ikajdan/katia/hardware/flash.kicad_sch

## KiCad design hardware/flash.kicad_sch (2026-06-07)

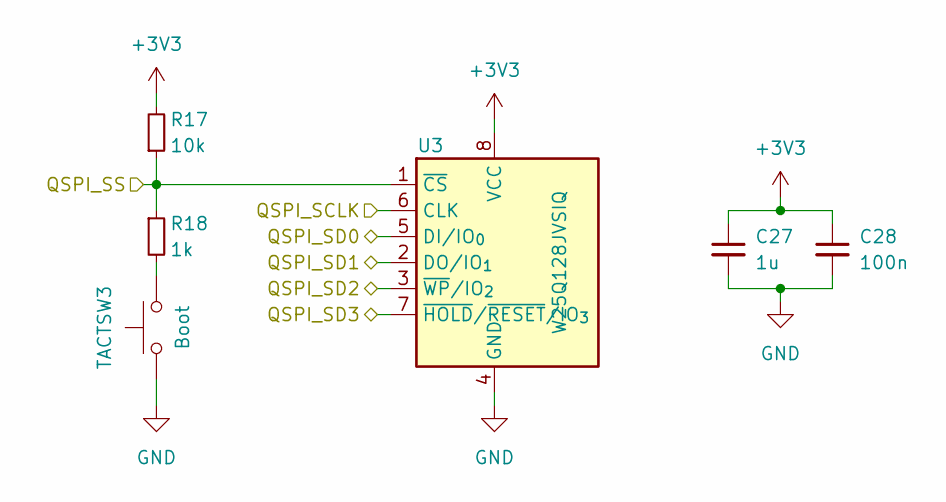
[picture p8: schematic flash.kicad_sch]

Parts:
C27: 1u; C_0603_1608Metric; JLCPCB Part # C15849
C28: 100n; C_0603_1608Metric; JLCPCB Part # C14663
R17: 10k; R_0603_1608Metric; JLCPCB Part # C98220
R18: 1k; R_0603_1608Metric; JLCPCB Part # C22548
TACTSW3: TS-1088R-02026; JLCPCB Part # C455280
U3: W25Q128JVSIQ; SOIC-8_5.3x5.3mm_P1.27mm; JLCPCB Part # C113767

Connections:
+3V3: C27.1, C28.1, R17.2, U3.8 (VCC)
GND: C27.2, C28.2, TACTSW3.1, U3.4 (GND)
unnamed: R18.2, TACTSW3.2
QSPI_SCLK: U3.6 (CLK)
QSPI_SD0: U3.5 (DI/IO_{0})
QSPI_SD1: U3.2 (DO/IO_{1})
QSPI_SD2: U3.3 (~WP/IO_{2})
QSPI_SD3: U3.7 (~HOLD/~RESET/IO_{3})
QSPI_SS: R17.1, R18.1, U3.1 (~CS)
