ikajdan/katia/hardware/leds.kicad_sch

## KiCad design hardware/leds.kicad_sch (2026-06-07)

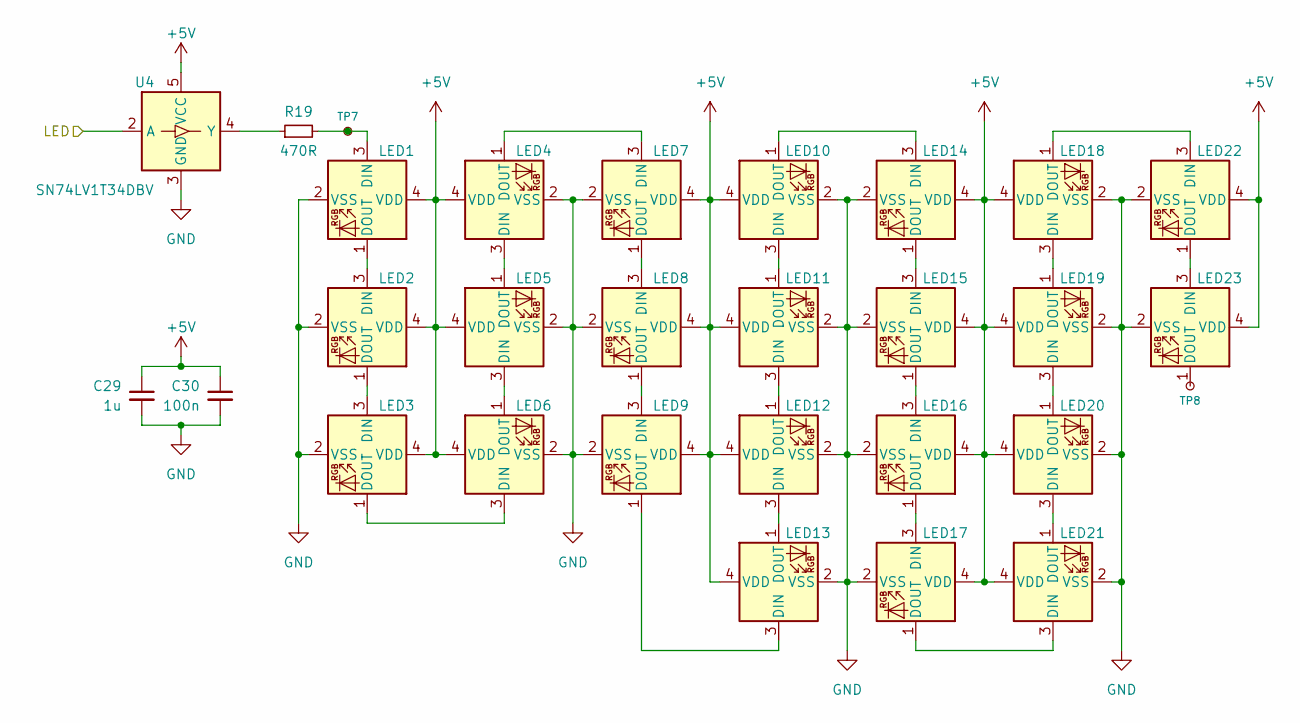
[picture p9: schematic leds.kicad_sch]

Parts:
C29: 1u; C_0603_1608Metric; JLCPCB Part # C15849
C30: 100n; C_0603_1608Metric; JLCPCB Part # C14663
LED1, LED2, LED3, LED4, LED5, LED6, LED7, LED8, LED9, LED10, LED11, LED12, LED13, LED14, LED15, LED16, LED17, LED18, LED19, LED20, LED21, LED22, LED23: YS-SK6812MINI-E; JLCPCB Part # C5149201
R19: 470R; R_0603_1608Metric; JLCPCB Part # C23179
TP7, TP8: TX; TestPoint_Pad_D1.0mm
U4: SN74LV1T34DBV; SOT-23-5; JLCPCB Part # C100024

Connections:
+5V: C29.1, C30.1, LED1.4 (VDD), LED2.4 (VDD), LED3.4 (VDD), LED4.4 (VDD), LED5.4 (VDD), LED6.4 (VDD), LED7.4 (VDD), LED8.4 (VDD), LED9.4 (VDD), LED10.4 (VDD), LED11.4 (VDD), LED12.4 (VDD), LED13.4 (VDD), LED14.4 (VDD), LED15.4 (VDD), LED16.4 (VDD), LED17.4 (VDD), LED18.4 (VDD), LED19.4 (VDD), LED20.4 (VDD), LED21.4 (VDD), LED22.4 (VDD), LED23.4 (VDD), U4.5 (VCC)
GND: C29.2, C30.2, LED1.2 (VSS), LED2.2 (VSS), LED3.2 (VSS), LED4.2 (VSS), LED5.2 (VSS), LED6.2 (VSS), LED7.2 (VSS), LED8.2 (VSS), LED9.2 (VSS), LED10.2 (VSS), LED11.2 (VSS), LED12.2 (VSS), LED13.2 (VSS), LED14.2 (VSS), LED15.2 (VSS), LED16.2 (VSS), LED17.2 (VSS), LED18.2 (VSS), LED19.2 (VSS), LED20.2 (VSS), LED21.2 (VSS), LED22.2 (VSS), LED23.2 (VSS), U4.3 (GND)
LED: U4.2 (A)
unnamed: LED1.1 (DOUT), LED2.3 (DIN)
unnamed: LED1.3 (DIN), R19.2, TP7.1
unnamed: LED2.1 (DOUT), LED3.3 (DIN)
unnamed: LED3.1 (DOUT), LED6.3 (DIN)
unnamed: LED4.1 (DOUT), LED7.3 (DIN)
unnamed: LED4.3 (DIN), LED5.1 (DOUT)
unnamed: LED5.3 (DIN), LED6.1 (DOUT)
unnamed: LED7.1 (DOUT), LED8.3 (DIN)
unnamed: LED8.1 (DOUT), LED9.3 (DIN)
unnamed: LED10.1 (DOUT), LED14.3 (DIN)
unnamed: LED10.3 (DIN), LED11.1 (DOUT)
unnamed: LED11.3 (DIN), LED12.1 (DOUT)
unnamed: LED12.3 (DIN), LED13.1 (DOUT)
unnamed: LED9.1 (DOUT), LED13.3 (DIN)
unnamed: LED14.1 (DOUT), LED15.3 (DIN)
unnamed: LED15.1 (DOUT), LED16.3 (DIN)
unnamed: LED16.1 (DOUT), LED17.3 (DIN)
unnamed: LED17.1 (DOUT), LED21.3 (DIN)
unnamed: LED18.1 (DOUT), LED22.3 (DIN)
unnamed: LED18.3 (DIN), LED19.1 (DOUT)
unnamed: LED19.3 (DIN), LED20.1 (DOUT)
unnamed: LED20.3 (DIN), LED21.1 (DOUT)
unnamed: LED22.1 (DOUT), LED23.3 (DIN)
unnamed: LED23.1 (DOUT), TP8.1
unnamed: R19.1, U4.4 (Y)
