ikajdan/katia/hardware/left_board.kicad_sch

## KiCad design hardware/left_board.kicad_sch (2026-06-07)

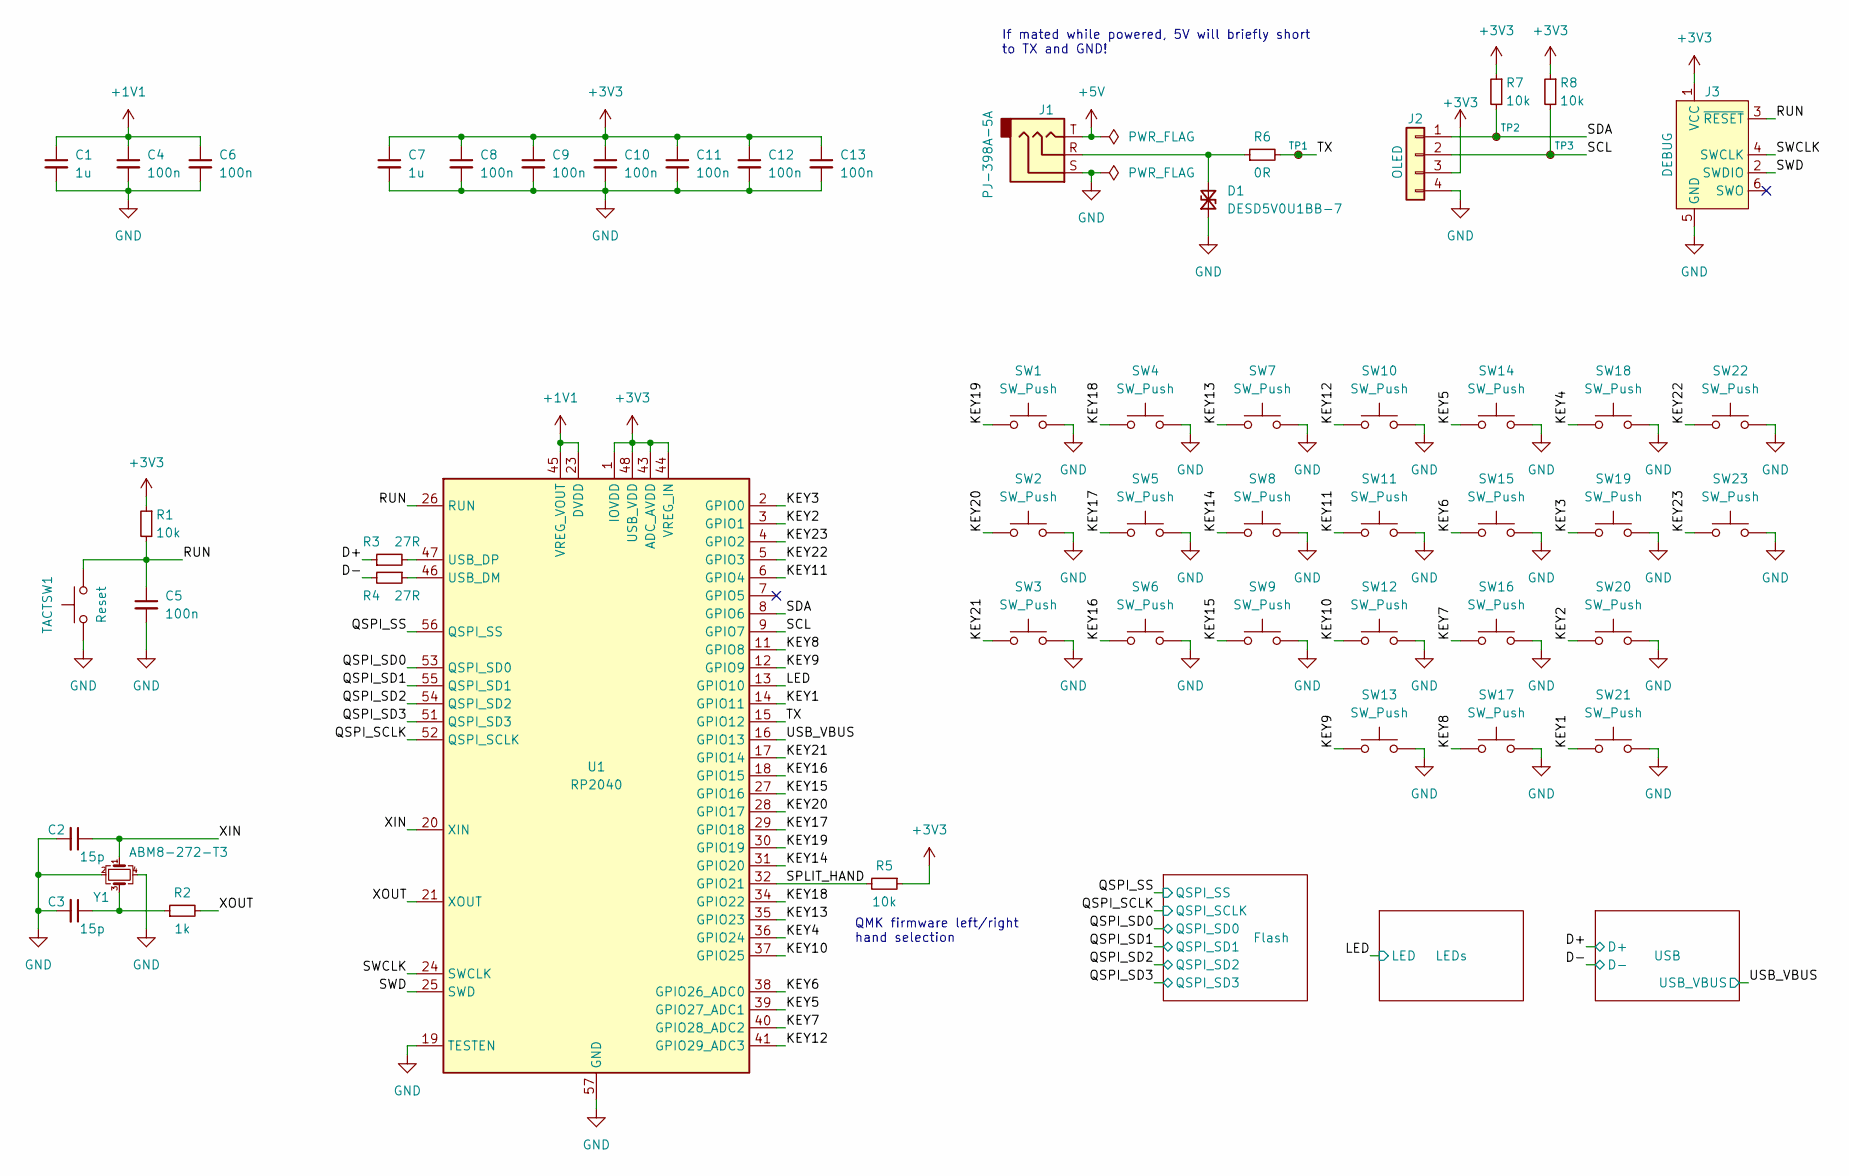
[picture p10: schematic left_board.kicad_sch]

Parts:
C1, C7: 1u; C_0603_1608Metric; JLCPCB Part # C15849
C2, C3: 15p; C_0603_1608Metric; JLCPCB Part # C1644
C4, C5, C6, C8, C9, C10, C11, C12, C13: 100n; C_0603_1608Metric; JLCPCB Part # C14663
D1: DESD5V0U1BB-7; D_SOD-523; JLCPCB Part # C3001672
J1: PJ-398A-5A; JLCPCB Part # C707238
J2: Conn_01x04; OLED_Screen
J3: TC2030-NL; Tag-Connect_TC2030-IDC-NL_2x03_P1.27mm_Vertical
R1, R5, R7, R8: 10k; R_0603_1608Metric; JLCPCB Part # C98220
R2: 1k; R_0603_1608Metric; JLCPCB Part # C22548
R3, R4: 27R; R_0603_1608Metric; JLCPCB Part # C25190
R6: 0R; R_0603_1608Metric; JLCPCB Part # C713447
SW1, SW2, SW3, SW4, SW5, SW6, SW7, SW8, SW9, SW10, SW11, SW12, SW13, SW14, SW15, SW16, SW17, SW18, SW19, SW20, SW22, SW23: SW_Push; SW_Cherry-MX_Hotswap_1u
SW21: SW_Push; SW_Cherry-MX_Hotswap_1.5u
TACTSW1: TS-1088R-02026; JLCPCB Part # C455280
TP1: TX; TestPoint_Pad_D1.0mm
TP2: SDA; TestPoint_Pad_D1.0mm
TP3: SCL; TestPoint_Pad_D1.0mm
U1: RP2040; QFN-56-1EP_7x7mm_P0.4mm_EP3.2x3.2mm; JLCPCB Part # C2040
Y1: ABM8-272-T3; Crystal_SMD_3225-4Pin_3.2x2.5mm; MFR.Part # Q22FA23V0041800; JLCPCB Part # C91749

Connections:
+1V1: C1.1, C4.1, C6.1, U1.23 (DVDD), U1.45 (VREG_VOUT), U1.50 (DVDD)
+3V3: C7.1, C8.1, C9.1, C10.1, C11.1, C12.1, C13.1, J2.3, J3.1 (VCC), R1.1, R5.1, R7.1, R8.1, U1.1 (IOVDD), U1.10 (IOVDD), U1.22 (IOVDD), U1.33 (IOVDD), U1.42 (IOVDD), U1.43 (ADC_AVDD), U1.44 (VREG_IN), U1.48 (USB_VDD), U1.49 (IOVDD)
+5V: J1.T
D+: R3.1
D-: R4.2
GND: C1.2, C2.2, C3.2, C4.2, C5.2, C6.2, C7.2, C8.2, C9.2, C10.2, C11.2, C12.2, C13.2, D1.1 (A1), J1.S, J2.4, J3.5 (GND), SW1.2, SW2.2, SW3.2, SW4.2, SW5.2, SW6.2, SW7.2, SW8.2, SW9.2, SW10.2, SW11.2, SW12.2, SW13.2, SW14.2, SW15.2, SW16.2, SW17.2, SW18.2, SW19.2, SW20.2, SW21.2, SW22.2, SW23.2, TACTSW1.1, U1.19 (TESTEN), U1.57 (GND), Y1.2, Y1.4
KEY1: SW21.1, U1.14 (GPIO11)
KEY2: SW20.1, U1.3 (GPIO1)
KEY3: SW19.1, U1.2 (GPIO0)
KEY4: SW18.1, U1.36 (GPIO24)
KEY5: SW14.1, U1.39 (GPIO27_ADC1)
KEY6: SW15.1, U1.38 (GPIO26_ADC0)
KEY7: SW16.1, U1.40 (GPIO28_ADC2)
KEY8: SW17.1, U1.11 (GPIO8)
KEY9: SW13.1, U1.12 (GPIO9)
KEY10: SW12.1, U1.37 (GPIO25)
KEY11: SW11.1, U1.6 (GPIO4)
KEY12: SW10.1, U1.41 (GPIO29_ADC3)
KEY13: SW7.1, U1.35 (GPIO23)
KEY14: SW8.1, U1.31 (GPIO20)
KEY15: SW9.1, U1.27 (GPIO16)
KEY16: SW6.1, U1.18 (GPIO15)
KEY17: SW5.1, U1.29 (GPIO18)
KEY18: SW4.1, U1.34 (GPIO22)
KEY19: SW1.1, U1.30 (GPIO19)
KEY20: SW2.1, U1.28 (GPIO17)
KEY21: SW3.1, U1.17 (GPIO14)
KEY22: SW22.1, U1.5 (GPIO3)
KEY23: SW23.1, U1.4 (GPIO2)
LED: U1.13 (GPIO10)
unnamed: C3.1, R2.1, Y1.3
unnamed: D1.2 (A2), J1.R, R6.1
unnamed: R3.2, U1.47 (USB_DP)
unnamed: R4.1, U1.46 (USB_DM)
QSPI_SCLK: U1.52 (QSPI_SCLK)
QSPI_SD0: U1.53 (QSPI_SD0)
QSPI_SD1: U1.55 (QSPI_SD1)
QSPI_SD2: U1.54 (QSPI_SD2)
QSPI_SD3: U1.51 (QSPI_SD3)
QSPI_SS: U1.56 (QSPI_SS)
RUN: C5.1, J3.3 (~RESET), R1.2, TACTSW1.2, U1.26 (RUN)
SCL: J2.2, R8.2, TP3.1, U1.9 (GPIO7)
SDA: J2.1, R7.2, TP2.1, U1.8 (GPIO6)
SPLIT_HAND: R5.2, U1.32 (GPIO21)
SWCLK: J3.4 (SWCLK), U1.24 (SWCLK)
SWD: J3.2 (SWDIO), U1.25 (SWD)
TX: R6.2, TP1.1, U1.15 (GPIO12)
USB_VBUS: U1.16 (GPIO13)
XIN: C2.1, U1.20 (XIN), Y1.1
XOUT: R2.2, U1.21 (XOUT)

Notes on the sheet:
If mated while powered, 5V will briefly short to TX and GND!
QMK firmware left/right hand selection
