ikajdan/katia/hardware/right_board.kicad_sch

## KiCad design hardware/right_board.kicad_sch (2026-06-07)

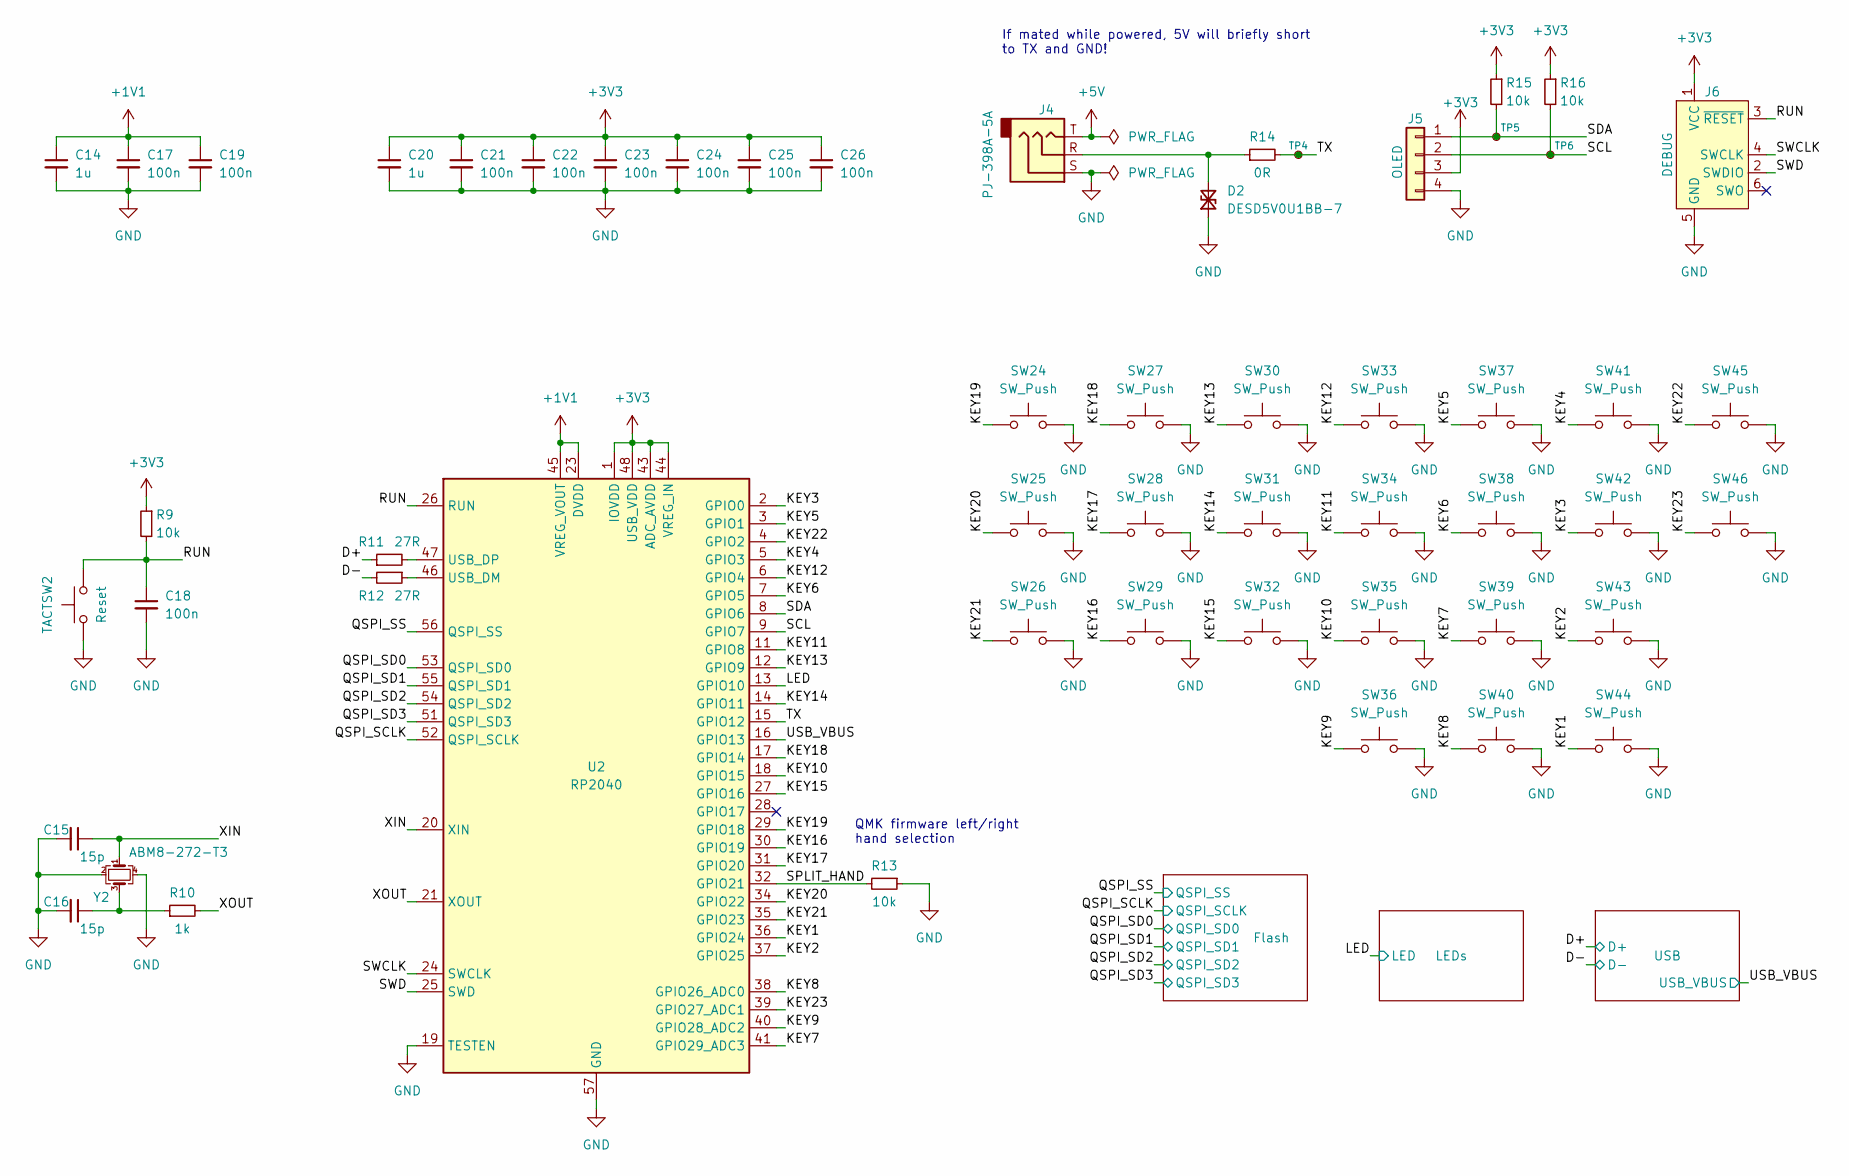
[picture p11: schematic right_board.kicad_sch]

Parts:
C14, C20: 1u; C_0603_1608Metric; JLCPCB Part # C15849
C15, C16: 15p; C_0603_1608Metric; JLCPCB Part # C1644
C17, C18, C19, C21, C22, C23, C24, C25, C26: 100n; C_0603_1608Metric; JLCPCB Part # C14663
D2: DESD5V0U1BB-7; D_SOD-523; JLCPCB Part # C3001672
J4: PJ-398A-5A; JLCPCB Part # C707238
J5: Conn_01x04; OLED_Screen
J6: TC2030-NL; Tag-Connect_TC2030-IDC-NL_2x03_P1.27mm_Vertical
R9, R13, R15, R16: 10k; R_0603_1608Metric; JLCPCB Part # C98220
R10: 1k; R_0603_1608Metric; JLCPCB Part # C22548
R11, R12: 27R; R_0603_1608Metric; JLCPCB Part # C25190
R14: 0R; R_0603_1608Metric; JLCPCB Part # C713447
SW24, SW25, SW26, SW27, SW28, SW29, SW30, SW31, SW32, SW33, SW34, SW35, SW36, SW37, SW38, SW39, SW40, SW41, SW42, SW43, SW45, SW46: SW_Push; SW_Cherry-MX_Hotswap_1u
SW44: SW_Push; SW_Cherry-MX_Hotswap_1.5u
TACTSW2: TS-1088R-02026; JLCPCB Part # C455280
TP4: TX; TestPoint_Pad_D1.0mm
TP5: SDA; TestPoint_Pad_D1.0mm
TP6: SCL; TestPoint_Pad_D1.0mm
U2: RP2040; QFN-56-1EP_7x7mm_P0.4mm_EP3.2x3.2mm; JLCPCB Part # C2040
Y2: ABM8-272-T3; Crystal_SMD_3225-4Pin_3.2x2.5mm; MFR.Part # Q22FA23V0041800; JLCPCB Part # C91749

Connections:
+1V1: C14.1, C17.1, C19.1, U2.23 (DVDD), U2.45 (VREG_VOUT), U2.50 (DVDD)
+3V3: C20.1, C21.1, C22.1, C23.1, C24.1, C25.1, C26.1, J5.3, J6.1 (VCC), R9.1, R15.1, R16.1, U2.1 (IOVDD), U2.10 (IOVDD), U2.22 (IOVDD), U2.33 (IOVDD), U2.42 (IOVDD), U2.43 (ADC_AVDD), U2.44 (VREG_IN), U2.48 (USB_VDD), U2.49 (IOVDD)
+5V: J4.T
D+: R11.1
D-: R12.2
GND: C14.2, C15.2, C16.2, C17.2, C18.2, C19.2, C20.2, C21.2, C22.2, C23.2, C24.2, C25.2, C26.2, D2.1 (A1), J4.S, J5.4, J6.5 (GND), R13.1, SW24.2, SW25.2, SW26.2, SW27.2, SW28.2, SW29.2, SW30.2, SW31.2, SW32.2, SW33.2, SW34.2, SW35.2, SW36.2, SW37.2, SW38.2, SW39.2, SW40.2, SW41.2, SW42.2, SW43.2, SW44.2, SW45.2, SW46.2, TACTSW2.1, U2.19 (TESTEN), U2.57 (GND), Y2.2, Y2.4
KEY1: SW44.1, U2.36 (GPIO24)
KEY2: SW43.1, U2.37 (GPIO25)
KEY3: SW42.1, U2.2 (GPIO0)
KEY4: SW41.1, U2.5 (GPIO3)
KEY5: SW37.1, U2.3 (GPIO1)
KEY6: SW38.1, U2.7 (GPIO5)
KEY7: SW39.1, U2.41 (GPIO29_ADC3)
KEY8: SW40.1, U2.38 (GPIO26_ADC0)
KEY9: SW36.1, U2.40 (GPIO28_ADC2)
KEY10: SW35.1, U2.18 (GPIO15)
KEY11: SW34.1, U2.11 (GPIO8)
KEY12: SW33.1, U2.6 (GPIO4)
KEY13: SW30.1, U2.12 (GPIO9)
KEY14: SW31.1, U2.14 (GPIO11)
KEY15: SW32.1, U2.27 (GPIO16)
KEY16: SW29.1, U2.30 (GPIO19)
KEY17: SW28.1, U2.31 (GPIO20)
KEY18: SW27.1, U2.17 (GPIO14)
KEY19: SW24.1, U2.29 (GPIO18)
KEY20: SW25.1, U2.34 (GPIO22)
KEY21: SW26.1, U2.35 (GPIO23)
KEY22: SW45.1, U2.4 (GPIO2)
KEY23: SW46.1, U2.39 (GPIO27_ADC1)
LED: U2.13 (GPIO10)
unnamed: C16.1, R10.1, Y2.3
unnamed: D2.2 (A2), J4.R, R14.1
unnamed: R11.2, U2.47 (USB_DP)
unnamed: R12.1, U2.46 (USB_DM)
QSPI_SCLK: U2.52 (QSPI_SCLK)
QSPI_SD0: U2.53 (QSPI_SD0)
QSPI_SD1: U2.55 (QSPI_SD1)
QSPI_SD2: U2.54 (QSPI_SD2)
QSPI_SD3: U2.51 (QSPI_SD3)
QSPI_SS: U2.56 (QSPI_SS)
RUN: C18.1, J6.3 (~RESET), R9.2, TACTSW2.2, U2.26 (RUN)
SCL: J5.2, R16.2, TP6.1, U2.9 (GPIO7)
SDA: J5.1, R15.2, TP5.1, U2.8 (GPIO6)
SPLIT_HAND: R13.2, U2.32 (GPIO21)
SWCLK: J6.4 (SWCLK), U2.24 (SWCLK)
SWD: J6.2 (SWDIO), U2.25 (SWD)
TX: R14.2, TP4.1, U2.15 (GPIO12)
USB_VBUS: U2.16 (GPIO13)
XIN: C15.1, U2.20 (XIN), Y2.1
XOUT: R10.2, U2.21 (XOUT)

Notes on the sheet:
If mated while powered, 5V will briefly short to TX and GND!
QMK firmware left/right hand selection
