ikajdan/katia/hardware/usb.kicad_sch

## KiCad design hardware/usb.kicad_sch (2026-06-07)

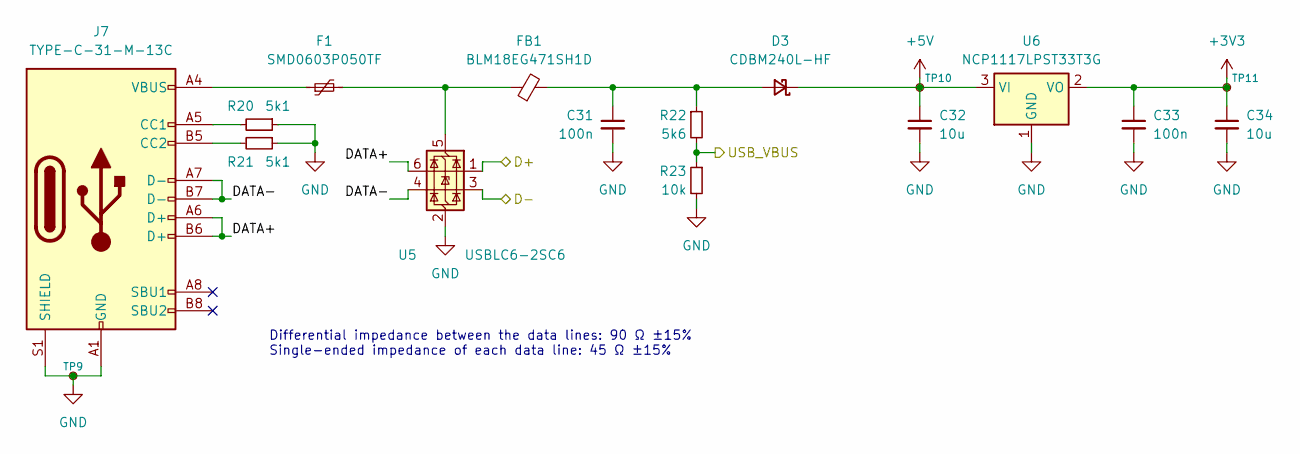
[picture p12: schematic usb.kicad_sch]

Parts:
C31, C33: 100n; C_0603_1608Metric; JLCPCB Part # C14663
C32, C34: 10u; C_0603_1608Metric; JLCPCB Part # C19702
D3: CDBM240L-HF; D_SOD-123; JLCPCB Part # C3012684
F1: SMD0603P050TF; Fuse_0603_1608Metric; JLCPCB Part # C20789
FB1: BLM18EG471SH1D; L_0603_1608Metric; JLCPCB Part # C440131
J7: TYPE-C-31-M-13C; JLCPCB Part # C2848620
R20, R21: 5k1; R_0603_1608Metric; JLCPCB Part # C2907044
R22: 5k6; R_0603_1608Metric; JLCPCB Part # C114627
R23: 10k; R_0603_1608Metric; JLCPCB Part # C98220
TP9: GND; TestPoint_Pad_D1.0mm
TP10: 5V; TestPoint_Pad_D1.0mm
TP11: 3V3; TestPoint_Pad_D1.0mm
U5: USBLC6-2SC6; SOT-23-6; JLCPCB Part # C7519
U6: NCP1117LPST33T3G; SOT-223-3_TabPin2; JLCPCB Part # C146799

Connections:
+3V3: C33.1, C34.1, TP11.1, U6.2 (VO)
+5V: C32.1, D3.1 (K), TP10.1, U6.3 (VI)
D+: U5.1 (I/O1)
D-: U5.3 (I/O2)
DATA+: J7.A6 (D+), J7.B6 (D+), U5.6 (I/O1)
DATA-: J7.A7 (D-), J7.B7 (D-), U5.4 (I/O2)
GND: C31.2, C32.2, C33.2, C34.2, J7.A1 (GND), J7.A12 (GND), J7.B1 (GND), J7.B12 (GND), J7.S1 (SHIELD), R20.1, R21.1, R23.2, TP9.1, U5.2 (GND), U6.1 (GND)
unnamed: C31.1, D3.2 (A), FB1.2, R22.1
unnamed: F1.1, J7.A4 (VBUS), J7.A9 (VBUS), J7.B4 (VBUS), J7.B9 (VBUS)
unnamed: F1.2, FB1.1, U5.5 (VBUS)
unnamed: J7.A5 (CC1), R20.2
unnamed: J7.B5 (CC2), R21.2
USB_VBUS: R22.2, R23.1

Notes on the sheet:
Differential impedance between the data lines: 90 Ω ±15% Single-ended impedance of each data line: 45 Ω ±15%
